hqrrr/arduino_project_anwendungswerkstatt/pictures/75dutycycle.png

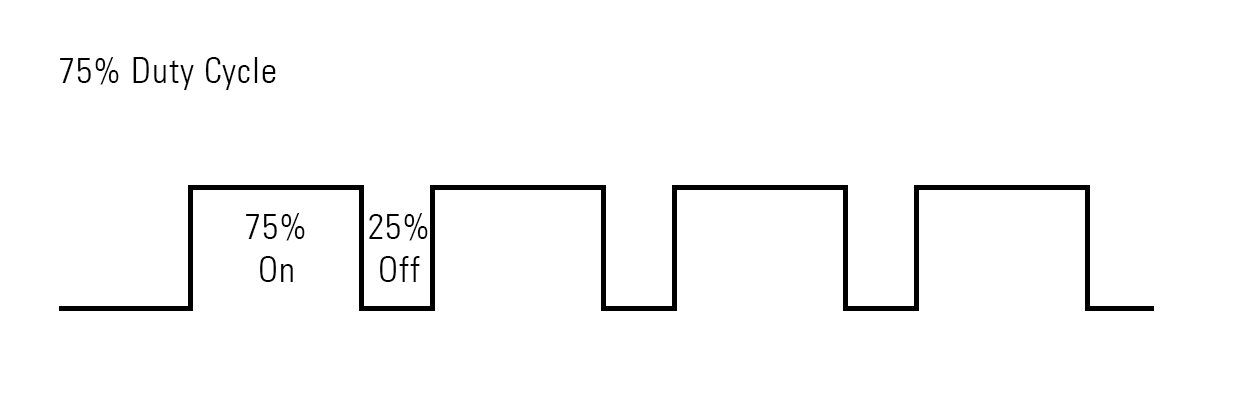
pictures/75dutycycle.png
