hqrrr/arduino_project_anwendungswerkstatt/pictures/arduino_multiple_DS18B20_13112020.png

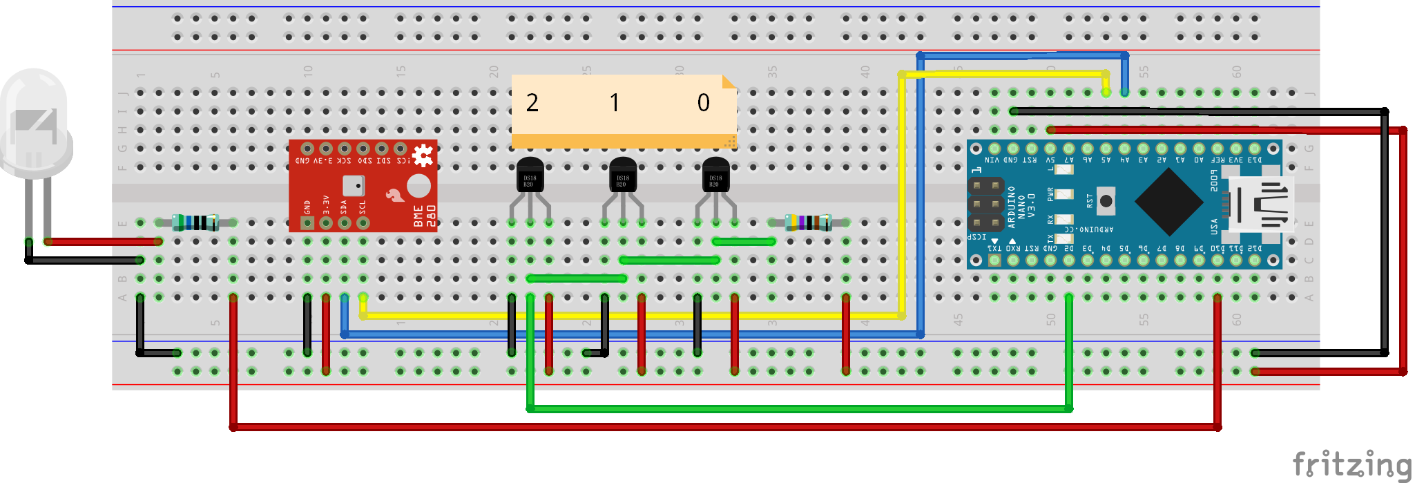
pictures/arduino_multiple_DS18B20_13112020.png
