hqrrr/arduino_project_anwendungswerkstatt/pictures/controlscreen.jpg

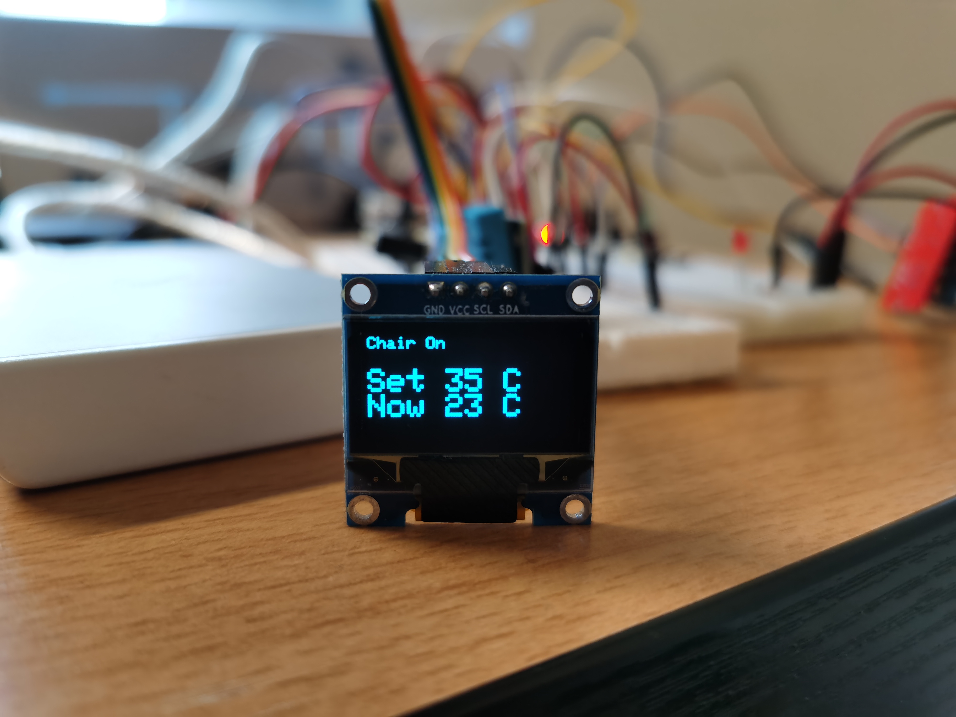
pictures/controlscreen.jpg
