hqrrr/arduino_project_anwendungswerkstatt/pictures/coronawarnung.jpg

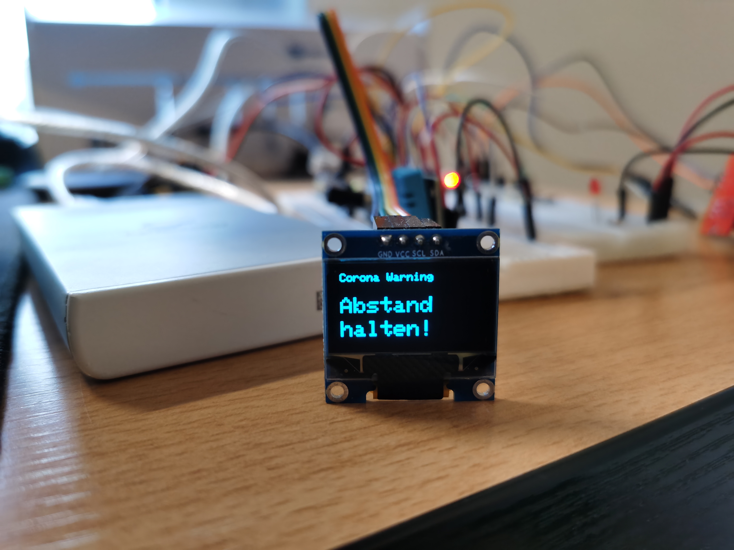
pictures/coronawarnung.jpg
