hqrrr/arduino_project_anwendungswerkstatt/pictures/I2CBus.png

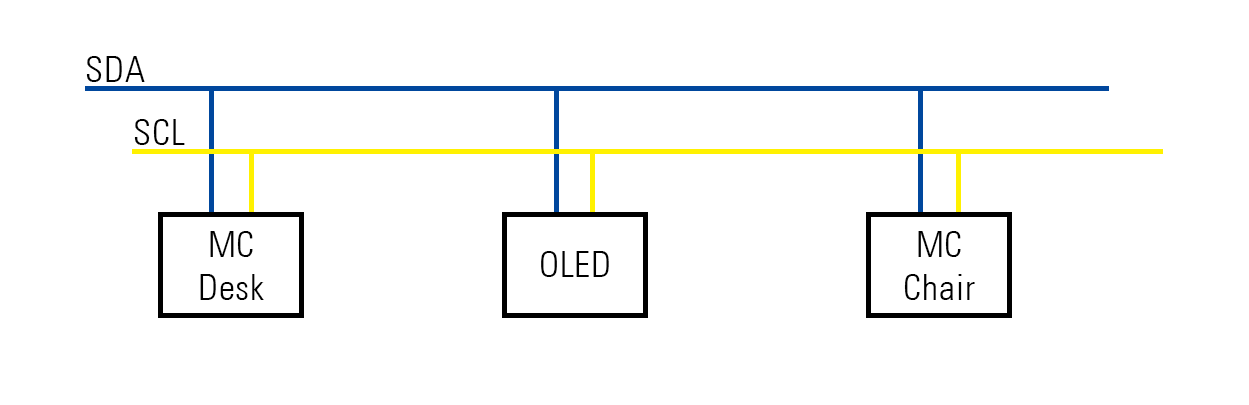
pictures/I2CBus.png
