hqrrr/arduino_project_anwendungswerkstatt/pictures/I2CBus_MC_communication.png

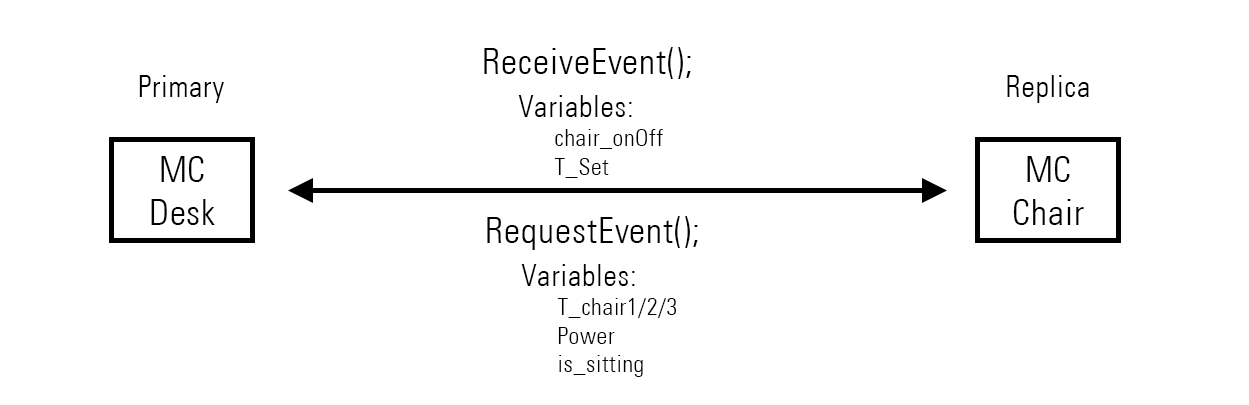
pictures/I2CBus_MC_communication.png
