hqrrr/arduino_project_anwendungswerkstatt/pictures/mosfet.png

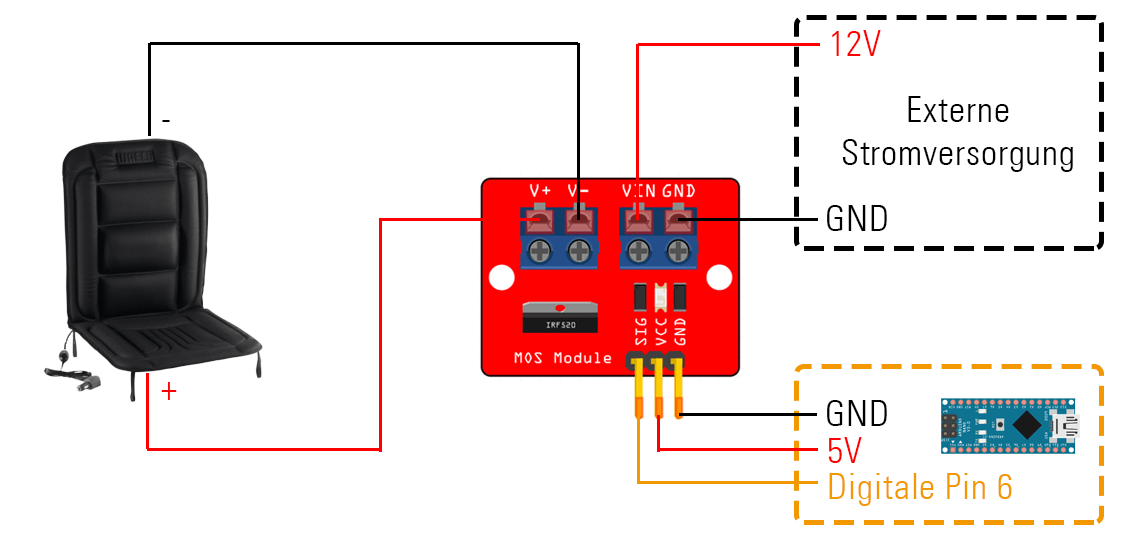
pictures/mosfet.png
