hqrrr/arduino_project_anwendungswerkstatt/pictures/OLED.png

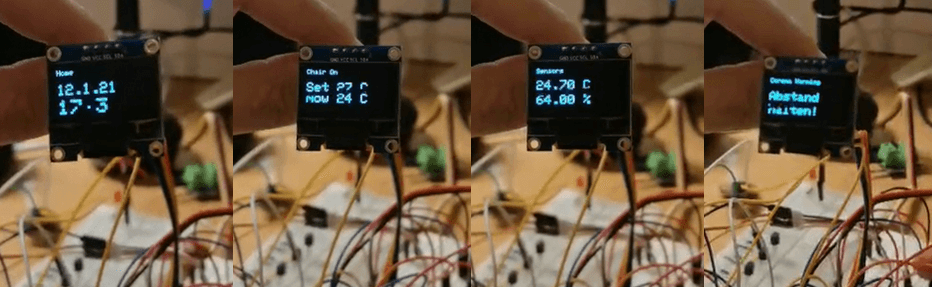
pictures/OLED.png
