hqrrr/arduino_project_anwendungswerkstatt/pictures/plot_demo.gif

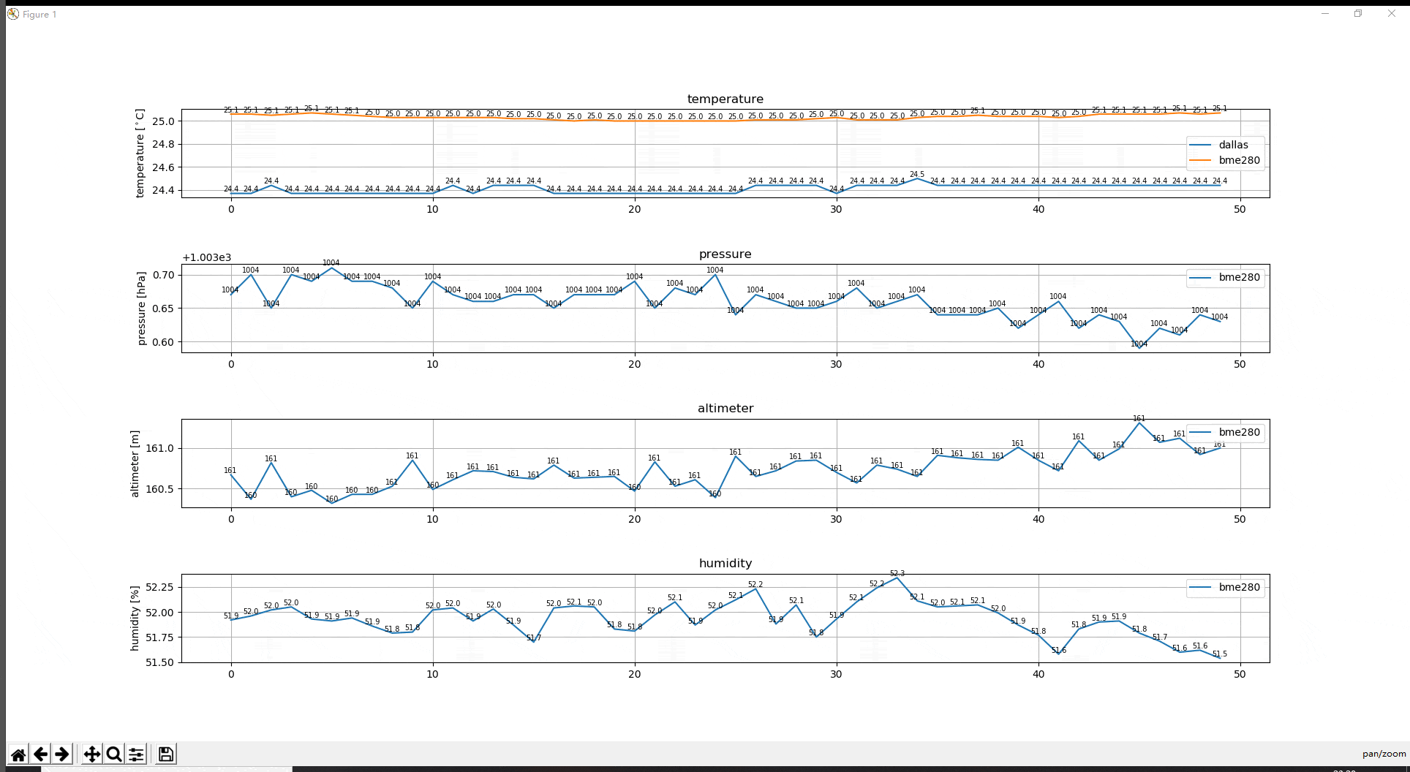
pictures/plot_demo.gif
