hqrrr/arduino_project_anwendungswerkstatt/pictures/sensescreen.jpg

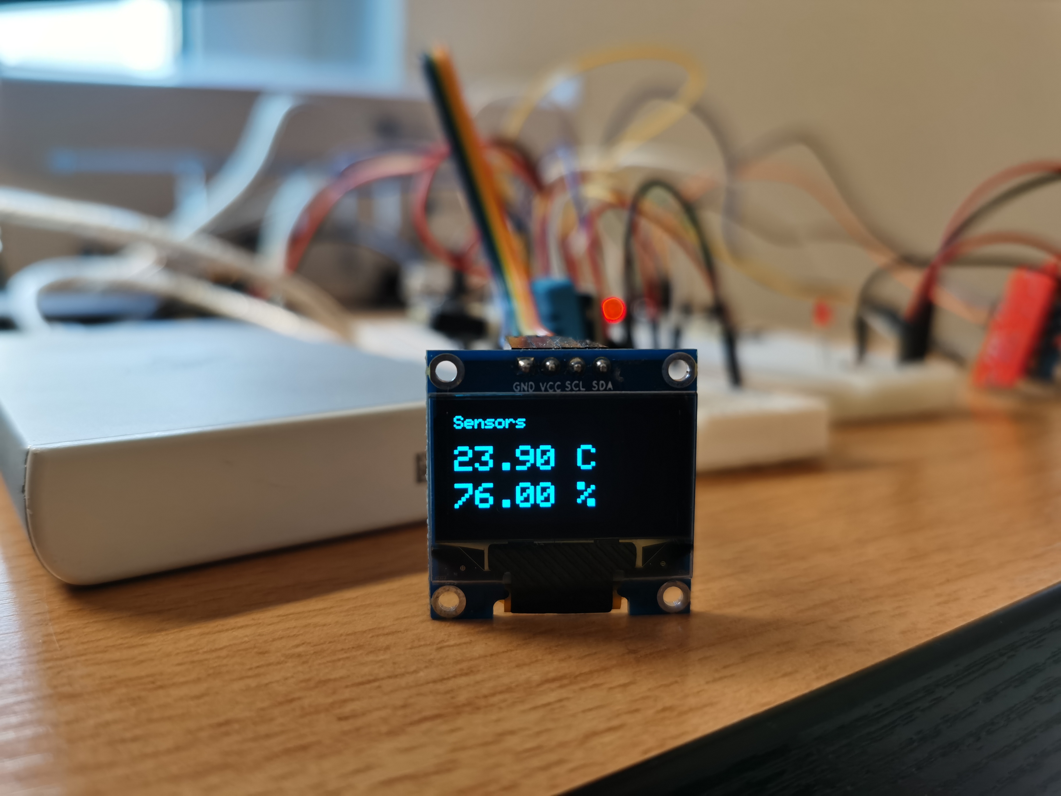
pictures/sensescreen.jpg
