hqrrr/arduino_project_anwendungswerkstatt/pictures/sketch.png

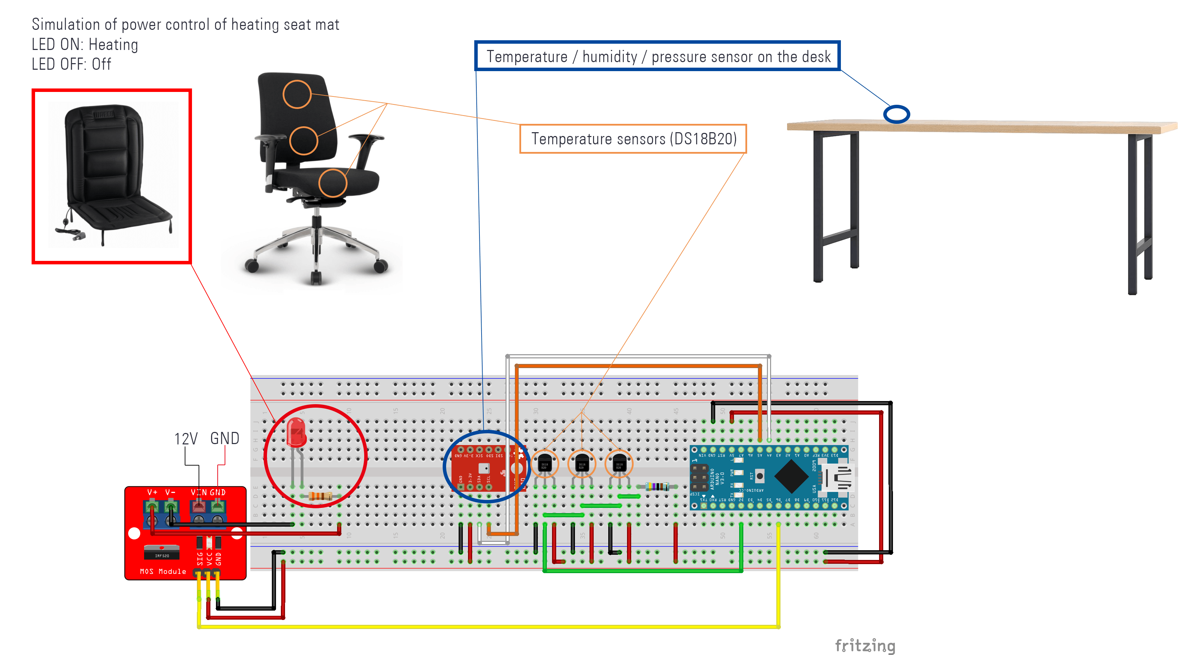
pictures/sketch.png
