hqrrr/arduino_project_anwendungswerkstatt/pictures/structure_I2C.png

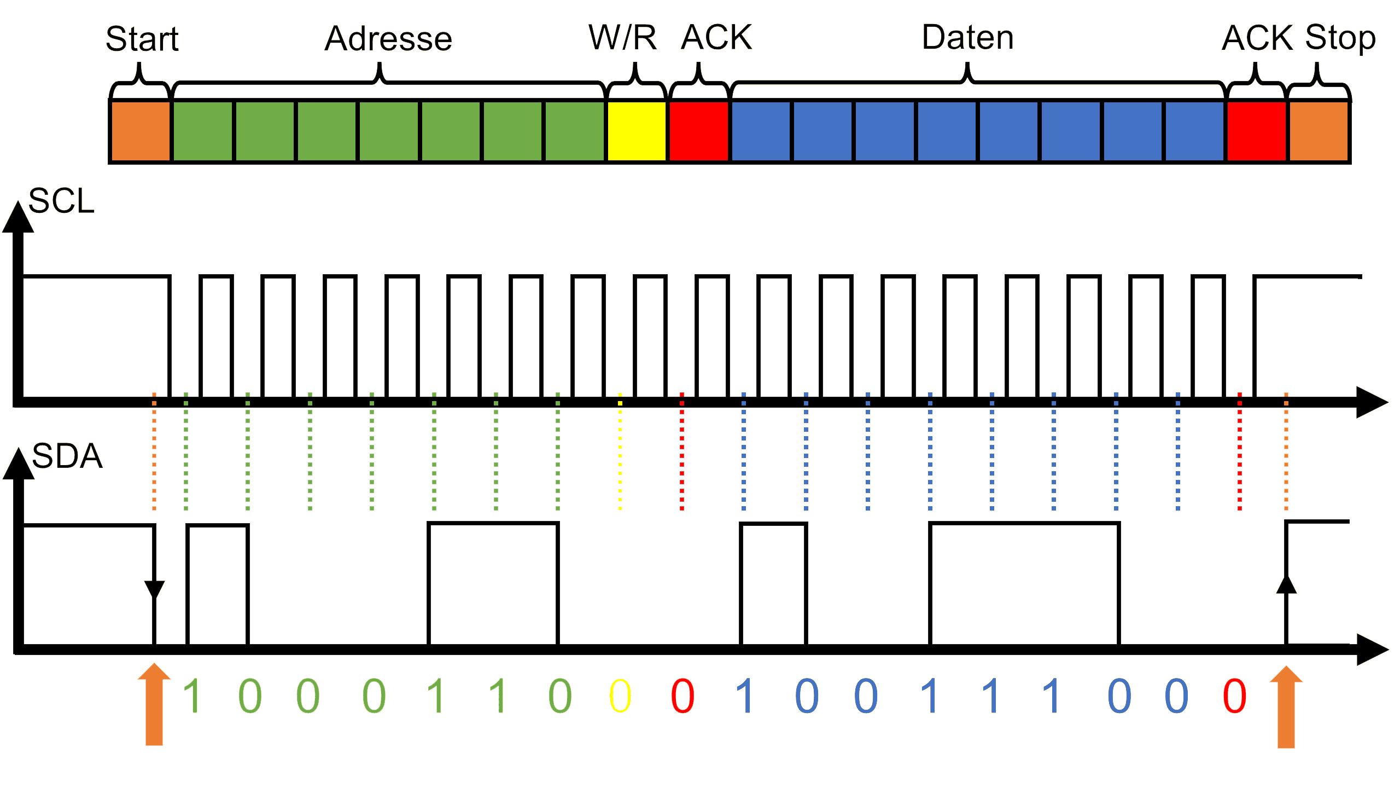
pictures/structure_I2C.png
