hqrrr/arduino_project_anwendungswerkstatt/pictures/DrucksensorAnleitung.PNG

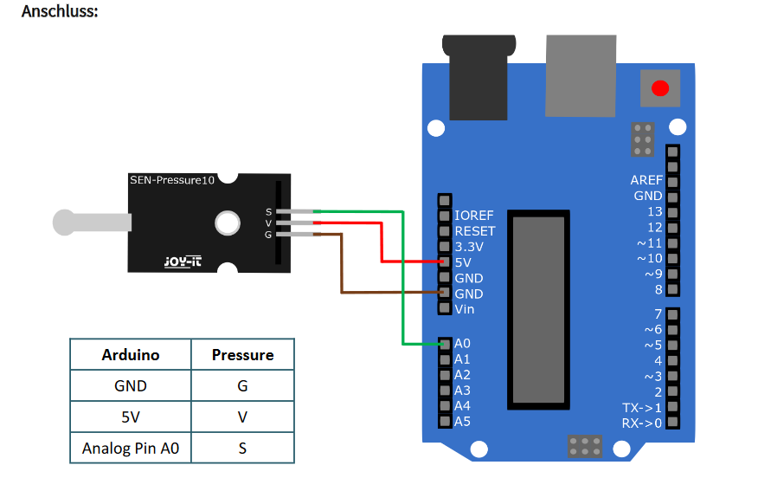
pictures/DrucksensorAnleitung.PNG
